iluvpomeranians/Acoustic_Imager/src/hardware/component_step_files/M4_Fan_screw_8mm.step

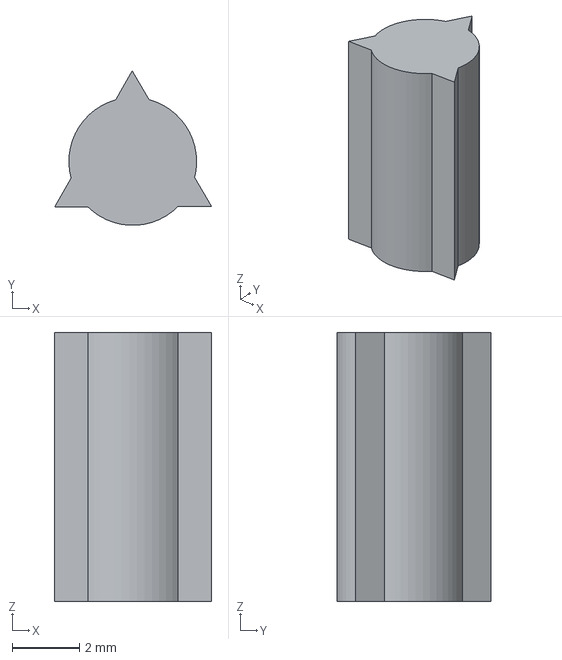
[picture p15: CAD file, 2026-03-14]
src/hardware/component_step_files/M4_Fan_screw_8mm.step
4.67 x 4.59 x 8.00 mm
