iluvpomeranians/Acoustic_Imager/src/hardware/component_step_files/M3.5x8mm Screw Hole Positive-Body.step

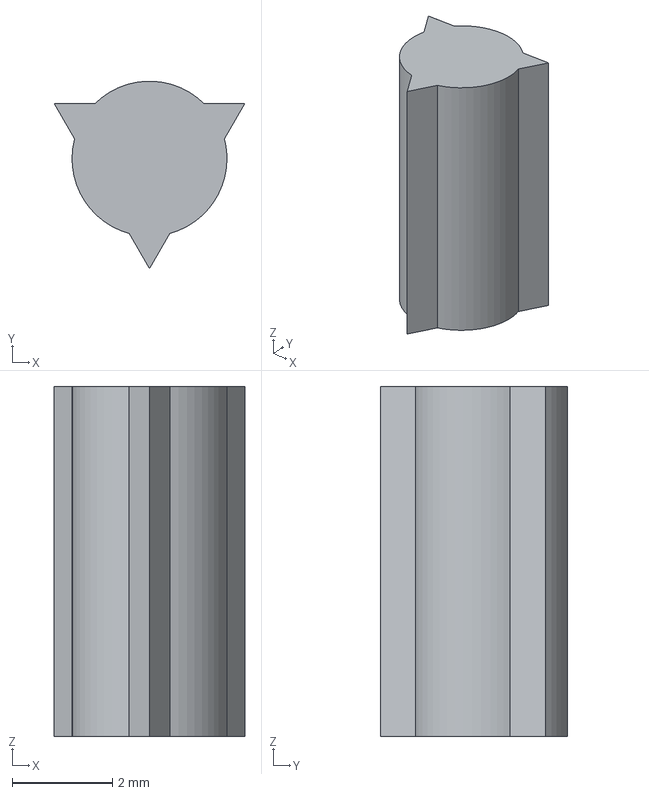
[picture p16: CAD file, 2026-03-14]
src/hardware/component_step_files/M3.5x8mm Screw Hole Positive-Body.step
3.81 x 3.75 x 7.00 mm
