iluvpomeranians/Acoustic_Imager/src/firmware/STM32G4_Cap/src/CubeMX/Core/Src/main.c

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
/* Includes ------------------------------------------------------------------*/
#include "main.h"
#include "adc.h"
#include "dma.h"
#include "spi.h"
#include "tim.h"
#include "usart.h"
#include "usb_device.h"
#include "gpio.h"

/* USER CODE BEGIN Includes */
#include "app_main.h"
/* USER CODE END Includes */


void SystemClock_Config(void);
/* USER CODE BEGIN 0 */


// HAL_SYSCFG_VREFBUF_HighImpedanceConfig(SYSCFG_VREFBUF_HIGH_IMPEDANCE_DISABLE);
// HAL_SYSCFG_EnableVREFBUF();
// IMPORTANT FOR ADC VALUES, DO NOT CHANGE
//C:\Users\Fabz\Desktop\aroundfuckin\Capstone_490_Software\src\firmware\STM32G4_Cap\src\CubeMX\Core\Src\stm32g4xx_hal_msp.c




/* USER CODE END 0 */

/**
  * @brief  The application entry point.
  * @retval int
  */
int main(void)
{

  /* MCU Configuration--------------------------------------------------------*/

  /* Reset of all peripherals, Initializes the Flash interface and the Systick. */
  HAL_Init();

  /* Configure the system clock */
  SystemClock_Config();

  /* USER CODE BEGIN SysInit */
  // TODO: TEST the UART and USB init
  /* USER CODE END SysInit */

  /* Initialize all configured peripherals */
  MX_GPIO_Init();
  MX_DMA_Init();
  MX_ADC1_Init();
  MX_ADC2_Init();
  MX_ADC3_Init();
  MX_ADC4_Init();
  MX_SPI4_Init();
  MX_TIM6_Init();
  MX_USART2_UART_Init();
  MX_USB_Device_Init();
  MX_ADC5_Init();
  /* USER CODE BEGIN 2 */
  app_init();
  app_start();
  /* USER CODE END 2 */

  /* Infinite loop */
  /* USER CODE BEGIN WHILE */
  while (1)
  {
    /* USER CODE END WHILE */

    /* USER CODE BEGIN 3 */
#if MODE == RELEASE | MODE == DEBUG
    app_loop();
#elif MODE == TEST_SPI_STREAM
    test_spi_stream_loop();
#elif MODE == TEST_DSP_PIPELINE
    test_dsp_pipeline_loop();
#endif
  }
  
  /* USER CODE END 3 */
}

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
