iluvpomeranians/Acoustic_Imager/src/firmware/STM32G4_Cap/src/CubeMX/App/app_main.h

#ifndef APP_MAIN_H
#define APP_MAIN_H

#ifdef __cplusplus
extern "C" {
#endif

/* =========================================================================
 * INCLUDES
 * ========================================================================= */
#include <stdint.h>
#include <stdbool.h>

/* =========================================================================
 * DEFINES
 * ========================================================================= */
#define APP_VERSION "1.0.0"

#define FRAME_SIZE 512
#define N_ADCS 4
#define N_CH_PER_ADC 4
#define N_MICS 16



// TODO: Consider discarding Nyquist bin (bin 512)
#define N_BINS ((FRAME_SIZE >> 1) + 1) // For real FFT: N_BINS = (N/2)+1 = 513 

#define APP_USB_CMD_MAX_LEN 64u

// Battery is measured through a 6:1 divider, so scale sensed pin voltage back to pack voltage.
#define BATT_ADC_VREF_MV 2900u
#define BATT_DIVIDER_NUMERATOR 5.97
#define BATT_DIVIDER_DENOMINATOR 1u

// Cycle-reduction options (see App/OPTIMIZATION_PLAN.md)
#define SPI_CHECKSUM_ENABLE       0   /* 0 = no checksum (~300k CC/frame saved); host must use header+payload only */
#define APP_BATTERY_READ_EVERY_N_FRAMES 8u   /* Read battery every N frames; use cached value otherwise (~100k CC saved when N>1) */
#define APP_CLIP_DETECT_ENABLE    0   /* 0 = skip time-domain clipping scan every frame */

// Configuration defines
#define SPI_SINGLE_MIC 0
#define SPI_FULL_FRAME 1
#define SPI_MODE SPI_FULL_FRAME

#define RELEASE 0
#define TEST_SPI_STREAM 1
#define TEST_DSP_PIPELINE 2
#define DEBUG 3

#define MODE RELEASE

// Float print helper macros
#define PRINT_F1(x) ((int)((x) * 10.0f) / 10),  ((int)((x) * 10.0f) % 10)
#define PRINT_F2(x) ((int)((x) * 100.0f) / 100), ((int)((x) * 100.0f) % 100)
#define PRINT_F3(x) ((int)((x) * 1000.0f) / 1000), ((int)((x) * 1000.0f) % 1000)

/* =========================================================================
 * TYPE DEFINITIONS
 * ========================================================================= */
typedef enum {
    APP_STATE_IDLE,
    APP_STATE_RUNNING,
    APP_STATE_ERROR
} app_state_t;

/* =========================================================================
 * FUNCTION PROTOTYPES
 * ========================================================================= */
void app_init(void);
void app_start(void);
void app_loop(void);
void app_usb_cdc_rx(const uint8_t *buf, uint32_t len);
// void app_handle_error(uint32_t error_code);

// Unit test loops
void test_spi_stream_loop(void);
void test_dsp_pipeline_loop(void);

#ifdef __cplusplus
}
#endif

#endif /* APP_MAIN_H */
