iluvpomeranians/Acoustic_Imager/src/firmware/STM32G4_Cap/src/CubeMX/Core/Inc/main.h

#define GAIN_CNTL_Pin GPIO_PIN_9
#define GAIN_CNTL_GPIO_Port GPIOD
#define BATT_SAMPLE_Pin GPIO_PIN_8
#define BATT_SAMPLE_GPIO_Port GPIOA
#define AUTO_GAIN_CNTL_Pin GPIO_PIN_9
#define AUTO_GAIN_CNTL_GPIO_Port GPIOB
#define MCU_STATUS_Pin GPIO_PIN_0
#define MCU_STATUS_GPIO_Port GPIOE
#define RPI_STATUS_Pin GPIO_PIN_1
#define RPI_STATUS_GPIO_Port GPIOE
