iluvpomeranians/Acoustic_Imager/src/firmware/STM32G4_Cap/src/CubeMX/Core/Src/adc.c

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
/* Includes ------------------------------------------------------------------*/
#include "adc.h"

/* USER CODE BEGIN 0 */
static volatile uint8_t adc_half_ready = 0;
static volatile uint8_t adc_full_ready = 0;

uint8_t ADC_HalfReady(void)      { return adc_half_ready; }
uint8_t ADC_FullReady(void)      { return adc_full_ready; }
void    ADC_ClearHalfReady(void) { adc_half_ready = 0; }
void    ADC_ClearFullReady(void) { adc_full_ready = 0; }

HAL_StatusTypeDef ADC_ReadBatteryRaw(uint16_t *raw_counts)
{
  if (!raw_counts) {
    return HAL_ERROR;
  }

  if (HAL_ADC_Start(&hadc5) != HAL_OK) {
    return HAL_ERROR;
  }

  if (HAL_ADC_PollForConversion(&hadc5, 10u) != HAL_OK) {
    (void)HAL_ADC_Stop(&hadc5);
    return HAL_TIMEOUT;
  }

  *raw_counts = (uint16_t)HAL_ADC_GetValue(&hadc5);
  return HAL_ADC_Stop(&hadc5);
}

/* USER CODE END 0 */

ADC_HandleTypeDef hadc1;
ADC_HandleTypeDef hadc2;
ADC_HandleTypeDef hadc3;
ADC_HandleTypeDef hadc4;
ADC_HandleTypeDef hadc5;
DMA_HandleTypeDef hdma_adc1;
DMA_HandleTypeDef hdma_adc2;
DMA_HandleTypeDef hdma_adc3;
DMA_HandleTypeDef hdma_adc4;

/* ADC1 init function */
void MX_ADC1_Init(void)
{

  ADC_MultiModeTypeDef multimode = {0};
  ADC_ChannelConfTypeDef sConfig = {0};

  /** Common config
  */
  hadc1.Instance = ADC1;
  hadc1.Init.ClockPrescaler = ADC_CLOCK_SYNC_PCLK_DIV4;
  hadc1.Init.Resolution = ADC_RESOLUTION_12B;
  hadc1.Init.DataAlign = ADC_DATAALIGN_RIGHT;
  hadc1.Init.GainCompensation = 0;
  hadc1.Init.ScanConvMode = ADC_SCAN_ENABLE;
  hadc1.Init.EOCSelection = ADC_EOC_SINGLE_CONV;
  hadc1.Init.LowPowerAutoWait = DISABLE;
  hadc1.Init.ContinuousConvMode = DISABLE;
  hadc1.Init.NbrOfConversion = 4;
  hadc1.Init.DiscontinuousConvMode = DISABLE;
  hadc1.Init.ExternalTrigConv = ADC_EXTERNALTRIG_T6_TRGO;
  hadc1.Init.ExternalTrigConvEdge = ADC_EXTERNALTRIGCONVEDGE_RISING;
  hadc1.Init.DMAContinuousRequests = ENABLE;
  hadc1.Init.Overrun = ADC_OVR_DATA_OVERWRITTEN;
  hadc1.Init.OversamplingMode = DISABLE;
  if (HAL_ADC_Init(&hadc1) != HAL_OK)
  {
    Error_Handler();
  }

  /** Configure the ADC multi-mode
  */
  multimode.Mode = ADC_MODE_INDEPENDENT;
  if (HAL_ADCEx_MultiModeConfigChannel(&hadc1, &multimode) != HAL_OK)
  {
    Error_Handler();
  }

  /** Configure Regular Channel
  */
  sConfig.Channel = ADC_CHANNEL_1;
  sConfig.Rank = ADC_REGULAR_RANK_1;
  sConfig.SamplingTime = ADC_SAMPLETIME_12CYCLES_5;
  sConfig.SingleDiff = ADC_SINGLE_ENDED;
  sConfig.OffsetNumber = ADC_OFFSET_NONE;
  sConfig.Offset = 0;
  if (HAL_ADC_ConfigChannel(&hadc1, &sConfig) != HAL_OK)
  {
    Error_Handler();
  }

  /** Configure Regular Channel
  */
  sConfig.Channel = ADC_CHANNEL_2;
  sConfig.Rank = ADC_REGULAR_RANK_2;
  if (HAL_ADC_ConfigChannel(&hadc1, &sConfig) != HAL_OK)
  {
    Error_Handler();
  }

  /** Configure Regular Channel
  */
  sConfig.Channel = ADC_CHANNEL_3;
  sConfig.Rank = ADC_REGULAR_RANK_3;
  if (HAL_ADC_ConfigChannel(&hadc1, &sConfig) != HAL_OK)
  {
    Error_Handler();
  }

  /** Configure Regular Channel
  */
  sConfig.Channel = ADC_CHANNEL_4;
  sConfig.Rank = ADC_REGULAR_RANK_4;
  if (HAL_ADC_ConfigChannel(&hadc1, &sConfig) != HAL_OK)
  {
    Error_Handler();
  }
}
/* ADC2 init function */
void MX_ADC2_Init(void)
{

  ADC_ChannelConfTypeDef sConfig = {0};

  /** Common config
  */
  hadc2.Instance = ADC2;
  hadc2.Init.ClockPrescaler = ADC_CLOCK_SYNC_PCLK_DIV4;
  hadc2.Init.Resolution = ADC_RESOLUTION_12B;
  hadc2.Init.DataAlign = ADC_DATAALIGN_RIGHT;
  hadc2.Init.GainCompensation = 0;
  hadc2.Init.ScanConvMode = ADC_SCAN_ENABLE;
  hadc2.Init.EOCSelection = ADC_EOC_SINGLE_CONV;
  hadc2.Init.LowPowerAutoWait = DISABLE;
  hadc2.Init.ContinuousConvMode = DISABLE;
  hadc2.Init.NbrOfConversion = 4;
  hadc2.Init.DiscontinuousConvMode = DISABLE;
  hadc2.Init.ExternalTrigConv = ADC_EXTERNALTRIG_T6_TRGO;
  hadc2.Init.ExternalTrigConvEdge = ADC_EXTERNALTRIGCONVEDGE_RISING;
  hadc2.Init.DMAContinuousRequests = ENABLE;
  hadc2.Init.Overrun = ADC_OVR_DATA_OVERWRITTEN;
  hadc2.Init.OversamplingMode = DISABLE;
  if (HAL_ADC_Init(&hadc2) != HAL_OK)
  {
    Error_Handler();
  }

  /** Configure Regular Channel
  */
  sConfig.Channel = ADC_CHANNEL_3;
  sConfig.Rank = ADC_REGULAR_RANK_1;
  sConfig.SamplingTime = ADC_SAMPLETIME_12CYCLES_5;
  sConfig.SingleDiff = ADC_SINGLE_ENDED;
  sConfig.OffsetNumber = ADC_OFFSET_NONE;
  sConfig.Offset = 0;
  if (HAL_ADC_ConfigChannel(&hadc2, &sConfig) != HAL_OK)
  {
    Error_Handler();
  }

  /** Configure Regular Channel
  */
  sConfig.Channel = ADC_CHANNEL_4;
  sConfig.Rank = ADC_REGULAR_RANK_2;
  if (HAL_ADC_ConfigChannel(&hadc2, &sConfig) != HAL_OK)
  {
    Error_Handler();
  }

  /** Configure Regular Channel
  */
  sConfig.Channel = ADC_CHANNEL_5;
  sConfig.Rank = ADC_REGULAR_RANK_3;
  if (HAL_ADC_ConfigChannel(&hadc2, &sConfig) != HAL_OK)
  {
    Error_Handler();
  }

  /** Configure Regular Channel
  */
  sConfig.Channel = ADC_CHANNEL_6;
  sConfig.Rank = ADC_REGULAR_RANK_4;
  if (HAL_ADC_ConfigChannel(&hadc2, &sConfig) != HAL_OK)
  {
    Error_Handler();
  }
}
/* ADC3 init function */
void MX_ADC3_Init(void)
{

  ADC_MultiModeTypeDef multimode = {0};
  ADC_ChannelConfTypeDef sConfig = {0};

  /** Common config
  */
  hadc3.Instance = ADC3;
  hadc3.Init.ClockPrescaler = ADC_CLOCK_SYNC_PCLK_DIV4;
  hadc3.Init.Resolution = ADC_RESOLUTION_12B;
  hadc3.Init.DataAlign = ADC_DATAALIGN_RIGHT;
  hadc3.Init.GainCompensation = 0;
  hadc3.Init.ScanConvMode = ADC_SCAN_ENABLE;
  hadc3.Init.EOCSelection = ADC_EOC_SINGLE_CONV;
  hadc3.Init.LowPowerAutoWait = DISABLE;
  hadc3.Init.ContinuousConvMode = DISABLE;
  hadc3.Init.NbrOfConversion = 4;
  hadc3.Init.DiscontinuousConvMode = DISABLE;
  hadc3.Init.ExternalTrigConv = ADC_EXTERNALTRIG_T6_TRGO;
  hadc3.Init.ExternalTrigConvEdge = ADC_EXTERNALTRIGCONVEDGE_RISING;
  hadc3.Init.DMAContinuousRequests = ENABLE;
  hadc3.Init.Overrun = ADC_OVR_DATA_OVERWRITTEN;
  hadc3.Init.OversamplingMode = DISABLE;
  if (HAL_ADC_Init(&hadc3) != HAL_OK)
  {
    Error_Handler();
  }

  /** Configure the ADC multi-mode
  */
  multimode.Mode = ADC_MODE_INDEPENDENT;
  if (HAL_ADCEx_MultiModeConfigChannel(&hadc3, &multimode) != HAL_OK)
  {
    Error_Handler();
  }

  /** Configure Regular Channel
  */
  sConfig.Channel = ADC_CHANNEL_1;
  sConfig.Rank = ADC_REGULAR_RANK_1;
  sConfig.SamplingTime = ADC_SAMPLETIME_12CYCLES_5;
  sConfig.SingleDiff = ADC_SINGLE_ENDED;
  sConfig.OffsetNumber = ADC_OFFSET_NONE;
  sConfig.Offset = 0;
  if (HAL_ADC_ConfigChannel(&hadc3, &sConfig) != HAL_OK)
  {
    Error_Handler();
  }

  /** Configure Regular Channel
  */
  sConfig.Channel = ADC_CHANNEL_2;
  sConfig.Rank = ADC_REGULAR_RANK_2;
  if (HAL_ADC_ConfigChannel(&hadc3, &sConfig) != HAL_OK)
  {
    Error_Handler();
  }

  /** Configure Regular Channel
  */
  sConfig.Channel = ADC_CHANNEL_3;
  sConfig.Rank = ADC_REGULAR_RANK_3;
  if (HAL_ADC_ConfigChannel(&hadc3, &sConfig) != HAL_OK)
  {
    Error_Handler();
  }

  /** Configure Regular Channel
  */
  sConfig.Channel = ADC_CHANNEL_4;
  sConfig.Rank = ADC_REGULAR_RANK_4;
  if (HAL_ADC_ConfigChannel(&hadc3, &sConfig) != HAL_OK)
  {
    Error_Handler();
  }
}
/* ADC4 init function */
void MX_ADC4_Init(void)
{

  ADC_ChannelConfTypeDef sConfig = {0};

  /** Common config
  */
  hadc4.Instance = ADC4;
  hadc4.Init.ClockPrescaler = ADC_CLOCK_SYNC_PCLK_DIV4;
  hadc4.Init.Resolution = ADC_RESOLUTION_12B;
  hadc4.Init.DataAlign = ADC_DATAALIGN_RIGHT;
  hadc4.Init.GainCompensation = 0;
  hadc4.Init.ScanConvMode = ADC_SCAN_ENABLE;
  hadc4.Init.EOCSelection = ADC_EOC_SINGLE_CONV;
  hadc4.Init.LowPowerAutoWait = DISABLE;
  hadc4.Init.ContinuousConvMode = DISABLE;
  hadc4.Init.NbrOfConversion = 4;
  hadc4.Init.DiscontinuousConvMode = DISABLE;
  hadc4.Init.ExternalTrigConv = ADC_EXTERNALTRIG_T6_TRGO;
  hadc4.Init.ExternalTrigConvEdge = ADC_EXTERNALTRIGCONVEDGE_RISING;
  hadc4.Init.DMAContinuousRequests = ENABLE;
  hadc4.Init.Overrun = ADC_OVR_DATA_OVERWRITTEN;
  hadc4.Init.OversamplingMode = DISABLE;
  if (HAL_ADC_Init(&hadc4) != HAL_OK)
  {
    Error_Handler();
  }

  /** Configure Regular Channel
  */
  sConfig.Channel = ADC_CHANNEL_1;
  sConfig.Rank = ADC_REGULAR_RANK_1;
  sConfig.SamplingTime = ADC_SAMPLETIME_12CYCLES_5;
  sConfig.SingleDiff = ADC_SINGLE_ENDED;
  sConfig.OffsetNumber = ADC_OFFSET_NONE;
  sConfig.Offset = 0;
  if (HAL_ADC_ConfigChannel(&hadc4, &sConfig) != HAL_OK)
  {
    Error_Handler();
  }

  /** Configure Regular Channel
  */
  sConfig.Channel = ADC_CHANNEL_2;
  sConfig.Rank = ADC_REGULAR_RANK_2;
  if (HAL_ADC_ConfigChannel(&hadc4, &sConfig) != HAL_OK)
  {
    Error_Handler();
  }

  /** Configure Regular Channel
  */
  sConfig.Channel = ADC_CHANNEL_3;
  sConfig.Rank = ADC_REGULAR_RANK_3;
  if (HAL_ADC_ConfigChannel(&hadc4, &sConfig) != HAL_OK)
  {
    Error_Handler();
  }

  /** Configure Regular Channel
  */
  sConfig.Channel = ADC_CHANNEL_4;
  sConfig.Rank = ADC_REGULAR_RANK_4;
  if (HAL_ADC_ConfigChannel(&hadc4, &sConfig) != HAL_OK)
  {
    Error_Handler();
  }
}
/* ADC5 init function */
void MX_ADC5_Init(void)
{

  ADC_ChannelConfTypeDef sConfig = {0};

  /** Common config
  */
  hadc5.Instance = ADC5;
  hadc5.Init.ClockPrescaler = ADC_CLOCK_SYNC_PCLK_DIV4;
  hadc5.Init.Resolution = ADC_RESOLUTION_12B;
  hadc5.Init.DataAlign = ADC_DATAALIGN_RIGHT;
  hadc5.Init.GainCompensation = 0;
  hadc5.Init.ScanConvMode = ADC_SCAN_DISABLE;
  hadc5.Init.EOCSelection = ADC_EOC_SINGLE_CONV;
  hadc5.Init.LowPowerAutoWait = DISABLE;
  hadc5.Init.ContinuousConvMode = DISABLE;
  hadc5.Init.NbrOfConversion = 1;
  hadc5.Init.DiscontinuousConvMode = DISABLE;
  hadc5.Init.ExternalTrigConv = ADC_SOFTWARE_START;
  hadc5.Init.ExternalTrigConvEdge = ADC_EXTERNALTRIGCONVEDGE_NONE;
  hadc5.Init.DMAContinuousRequests = DISABLE;
  hadc5.Init.Overrun = ADC_OVR_DATA_PRESERVED;
  hadc5.Init.OversamplingMode = DISABLE;
  if (HAL_ADC_Init(&hadc5) != HAL_OK)
  {
    Error_Handler();
  }

  /** Configure Regular Channel
  */
  sConfig.Channel = ADC_CHANNEL_1;
  sConfig.Rank = ADC_REGULAR_RANK_1;
  sConfig.SamplingTime = ADC_SAMPLETIME_2CYCLES_5;
  sConfig.SingleDiff = ADC_SINGLE_ENDED;
  sConfig.OffsetNumber = ADC_OFFSET_NONE;
  sConfig.Offset = 0;
  if (HAL_ADC_ConfigChannel(&hadc5, &sConfig) != HAL_OK)
  {
    Error_Handler();
  }
}

static uint32_t HAL_RCC_ADC12_CLK_ENABLED=0;
static uint32_t HAL_RCC_ADC345_CLK_ENABLED=0;

void HAL_ADC_MspInit(ADC_HandleTypeDef* adcHandle)
{

  GPIO_InitTypeDef GPIO_InitStruct = {0};
  RCC_PeriphCLKInitTypeDef PeriphClkInit = {0};
  if(adcHandle->Instance==ADC1)
  {
  /** Initializes the peripherals clocks
  */
    PeriphClkInit.PeriphClockSelection = RCC_PERIPHCLK_ADC12;
    PeriphClkInit.Adc12ClockSelection = RCC_ADC12CLKSOURCE_SYSCLK;
    if (HAL_RCCEx_PeriphCLKConfig(&PeriphClkInit) != HAL_OK)
    {
      Error_Handler();
    }

    /* ADC1 clock enable */
    HAL_RCC_ADC12_CLK_ENABLED++;
    if(HAL_RCC_ADC12_CLK_ENABLED==1){
      __HAL_RCC_ADC12_CLK_ENABLE();
    }

    __HAL_RCC_GPIOA_CLK_ENABLE();
    /**ADC1 GPIO Configuration
    PA0     ------> ADC1_IN1
    PA1     ------> ADC1_IN2
    PA2     ------> ADC1_IN3
    PA3     ------> ADC1_IN4
    */
    GPIO_InitStruct.Pin = GPIO_PIN_0|GPIO_PIN_1|GPIO_PIN_2|GPIO_PIN_3;
    GPIO_InitStruct.Mode = GPIO_MODE_ANALOG;
    GPIO_InitStruct.Pull = GPIO_NOPULL;
    HAL_GPIO_Init(GPIOA, &GPIO_InitStruct);

    /* ADC1 DMA Init */
    /* ADC1 Init */
    hdma_adc1.Instance = DMA1_Channel1;
    hdma_adc1.Init.Request = DMA_REQUEST_ADC1;
    hdma_adc1.Init.Direction = DMA_PERIPH_TO_MEMORY;
    hdma_adc1.Init.PeriphInc = DMA_PINC_DISABLE;
    hdma_adc1.Init.MemInc = DMA_MINC_ENABLE;
    hdma_adc1.Init.PeriphDataAlignment = DMA_PDATAALIGN_HALFWORD;
    hdma_adc1.Init.MemDataAlignment = DMA_MDATAALIGN_HALFWORD;
    hdma_adc1.Init.Mode = DMA_CIRCULAR;
    hdma_adc1.Init.Priority = DMA_PRIORITY_LOW;
    if (HAL_DMA_Init(&hdma_adc1) != HAL_OK)
    {
      Error_Handler();
    }

    __HAL_LINKDMA(adcHandle,DMA_Handle,hdma_adc1);

    /* ADC1 interrupt Init */
    HAL_NVIC_SetPriority(ADC1_2_IRQn, 0, 0);
    HAL_NVIC_EnableIRQ(ADC1_2_IRQn);
  }
  else if(adcHandle->Instance==ADC2)
  {
  /** Initializes the peripherals clocks
  */
    PeriphClkInit.PeriphClockSelection = RCC_PERIPHCLK_ADC12;
    PeriphClkInit.Adc12ClockSelection = RCC_ADC12CLKSOURCE_SYSCLK;
    if (HAL_RCCEx_PeriphCLKConfig(&PeriphClkInit) != HAL_OK)
    {
      Error_Handler();
    }

    /* ADC2 clock enable */
    HAL_RCC_ADC12_CLK_ENABLED++;
    if(HAL_RCC_ADC12_CLK_ENABLED==1){
      __HAL_RCC_ADC12_CLK_ENABLE();
    }

    __HAL_RCC_GPIOC_CLK_ENABLE();
    __HAL_RCC_GPIOA_CLK_ENABLE();
    /**ADC2 GPIO Configuration
    PC0     ------> ADC2_IN6
    PA6     ------> ADC2_IN3
    PA7     ------> ADC2_IN4
    PC4     ------> ADC2_IN5
    */
    GPIO_InitStruct.Pin = GPIO_PIN_0|GPIO_PIN_4;
    GPIO_InitStruct.Mode = GPIO_MODE_ANALOG;
    GPIO_InitStruct.Pull = GPIO_NOPULL;
    HAL_GPIO_Init(GPIOC, &GPIO_InitStruct);

    GPIO_InitStruct.Pin = GPIO_PIN_6|GPIO_PIN_7;
    GPIO_InitStruct.Mode = GPIO_MODE_ANALOG;
    GPIO_InitStruct.Pull = GPIO_NOPULL;
    HAL_GPIO_Init(GPIOA, &GPIO_InitStruct);

    /* ADC2 DMA Init */
    /* ADC2 Init */
    hdma_adc2.Instance = DMA1_Channel2;
    hdma_adc2.Init.Request = DMA_REQUEST_ADC2;
    hdma_adc2.Init.Direction = DMA_PERIPH_TO_MEMORY;
    hdma_adc2.Init.PeriphInc = DMA_PINC_DISABLE;
    hdma_adc2.Init.MemInc = DMA_MINC_ENABLE;
    hdma_adc2.Init.PeriphDataAlignment = DMA_PDATAALIGN_HALFWORD;
    hdma_adc2.Init.MemDataAlignment = DMA_MDATAALIGN_HALFWORD;
    hdma_adc2.Init.Mode = DMA_CIRCULAR;
    hdma_adc2.Init.Priority = DMA_PRIORITY_LOW;
    if (HAL_DMA_Init(&hdma_adc2) != HAL_OK)
    {
      Error_Handler();
    }

    __HAL_LINKDMA(adcHandle,DMA_Handle,hdma_adc2);

    /* ADC2 interrupt Init */
    HAL_NVIC_SetPriority(ADC1_2_IRQn, 0, 0);
    HAL_NVIC_EnableIRQ(ADC1_2_IRQn);
  }
  else if(adcHandle->Instance==ADC3)
  {
  /** Initializes the peripherals clocks
  */
    PeriphClkInit.PeriphClockSelection = RCC_PERIPHCLK_ADC345;
    PeriphClkInit.Adc345ClockSelection = RCC_ADC345CLKSOURCE_SYSCLK;
    if (HAL_RCCEx_PeriphCLKConfig(&PeriphClkInit) != HAL_OK)
    {
      Error_Handler();
    }

    /* ADC3 clock enable */
    HAL_RCC_ADC345_CLK_ENABLED++;
    if(HAL_RCC_ADC345_CLK_ENABLED==1){
      __HAL_RCC_ADC345_CLK_ENABLE();
    }

    __HAL_RCC_GPIOB_CLK_ENABLE();
    __HAL_RCC_GPIOE_CLK_ENABLE();
    /**ADC3 GPIO Configuration
    PB1     ------> ADC3_IN1
    PE7     ------> ADC3_IN4
    PE9     ------> ADC3_IN2
    PE13     ------> ADC3_IN3
    */
    GPIO_InitStruct.Pin = GPIO_PIN_1;
    GPIO_InitStruct.Mode = GPIO_MODE_ANALOG;
    GPIO_InitStruct.Pull = GPIO_NOPULL;
    HAL_GPIO_Init(GPIOB, &GPIO_InitStruct);

    GPIO_InitStruct.Pin = GPIO_PIN_7|GPIO_PIN_9|GPIO_PIN_13;
    GPIO_InitStruct.Mode = GPIO_MODE_ANALOG;
    GPIO_InitStruct.Pull = GPIO_NOPULL;
    HAL_GPIO_Init(GPIOE, &GPIO_InitStruct);

    /* ADC3 DMA Init */
    /* ADC3 Init */
    hdma_adc3.Instance = DMA1_Channel3;
    hdma_adc3.Init.Request = DMA_REQUEST_ADC3;
    hdma_adc3.Init.Direction = DMA_PERIPH_TO_MEMORY;
    hdma_adc3.Init.PeriphInc = DMA_PINC_DISABLE;
    hdma_adc3.Init.MemInc = DMA_MINC_ENABLE;
    hdma_adc3.Init.PeriphDataAlignment = DMA_PDATAALIGN_HALFWORD;
    hdma_adc3.Init.MemDataAlignment = DMA_MDATAALIGN_HALFWORD;
    hdma_adc3.Init.Mode = DMA_CIRCULAR;
    hdma_adc3.Init.Priority = DMA_PRIORITY_LOW;
    if (HAL_DMA_Init(&hdma_adc3) != HAL_OK)
    {
      Error_Handler();
    }

    __HAL_LINKDMA(adcHandle,DMA_Handle,hdma_adc3);

    /* ADC3 interrupt Init */
    HAL_NVIC_SetPriority(ADC3_IRQn, 0, 0);
    HAL_NVIC_EnableIRQ(ADC3_IRQn);
  }
  else if(adcHandle->Instance==ADC4)
  {
  /** Initializes the peripherals clocks
  */
    PeriphClkInit.PeriphClockSelection = RCC_PERIPHCLK_ADC345;
    PeriphClkInit.Adc345ClockSelection = RCC_ADC345CLKSOURCE_SYSCLK;
    if (HAL_RCCEx_PeriphCLKConfig(&PeriphClkInit) != HAL_OK)
    {
      Error_Handler();
    }

    /* ADC4 clock enable */
    HAL_RCC_ADC345_CLK_ENABLED++;
    if(HAL_RCC_ADC345_CLK_ENABLED==1){
      __HAL_RCC_ADC345_CLK_ENABLE();
    }

    __HAL_RCC_GPIOE_CLK_ENABLE();
    __HAL_RCC_GPIOB_CLK_ENABLE();
    /**ADC4 GPIO Configuration
    PE14     ------> ADC4_IN1
    PE15     ------> ADC4_IN2
    PB12     ------> ADC4_IN3
    PB14     ------> ADC4_IN4
    */
    GPIO_InitStruct.Pin = GPIO_PIN_14|GPIO_PIN_15;
    GPIO_InitStruct.Mode = GPIO_MODE_ANALOG;
    GPIO_InitStruct.Pull = GPIO_NOPULL;
    HAL_GPIO_Init(GPIOE, &GPIO_InitStruct);

    GPIO_InitStruct.Pin = GPIO_PIN_12|GPIO_PIN_14;
    GPIO_InitStruct.Mode = GPIO_MODE_ANALOG;
    GPIO_InitStruct.Pull = GPIO_NOPULL;
    HAL_GPIO_Init(GPIOB, &GPIO_InitStruct);

    /* ADC4 DMA Init */
    /* ADC4 Init */
    hdma_adc4.Instance = DMA1_Channel4;
    hdma_adc4.Init.Request = DMA_REQUEST_ADC4;
    hdma_adc4.Init.Direction = DMA_PERIPH_TO_MEMORY;
    hdma_adc4.Init.PeriphInc = DMA_PINC_DISABLE;
    hdma_adc4.Init.MemInc = DMA_MINC_ENABLE;
    hdma_adc4.Init.PeriphDataAlignment = DMA_PDATAALIGN_HALFWORD;
    hdma_adc4.Init.MemDataAlignment = DMA_MDATAALIGN_HALFWORD;
    hdma_adc4.Init.Mode = DMA_CIRCULAR;
    hdma_adc4.Init.Priority = DMA_PRIORITY_LOW;
    if (HAL_DMA_Init(&hdma_adc4) != HAL_OK)
    {
      Error_Handler();
    }

    __HAL_LINKDMA(adcHandle,DMA_Handle,hdma_adc4);

    /* ADC4 interrupt Init */
    HAL_NVIC_SetPriority(ADC4_IRQn, 0, 0);
    HAL_NVIC_EnableIRQ(ADC4_IRQn);
  }
  else if(adcHandle->Instance==ADC5)
  {
  /** Initializes the peripherals clocks
  */
    PeriphClkInit.PeriphClockSelection = RCC_PERIPHCLK_ADC345;
    PeriphClkInit.Adc345ClockSelection = RCC_ADC345CLKSOURCE_SYSCLK;
    if (HAL_RCCEx_PeriphCLKConfig(&PeriphClkInit) != HAL_OK)
    {
      Error_Handler();
    }

    /* ADC5 clock enable */
    HAL_RCC_ADC345_CLK_ENABLED++;
    if(HAL_RCC_ADC345_CLK_ENABLED==1){
      __HAL_RCC_ADC345_CLK_ENABLE();
    }

    __HAL_RCC_GPIOA_CLK_ENABLE();
    /**ADC5 GPIO Configuration
    PA8     ------> ADC5_IN1
    */
    GPIO_InitStruct.Pin = BATT_SAMPLE_Pin;
    GPIO_InitStruct.Mode = GPIO_MODE_ANALOG;
    GPIO_InitStruct.Pull = GPIO_NOPULL;
    HAL_GPIO_Init(BATT_SAMPLE_GPIO_Port, &GPIO_InitStruct);

  }
}

void HAL_ADC_MspDeInit(ADC_HandleTypeDef* adcHandle)
{

  if(adcHandle->Instance==ADC1)
  {
    /* Peripheral clock disable */
    HAL_RCC_ADC12_CLK_ENABLED--;
    if(HAL_RCC_ADC12_CLK_ENABLED==0){
      __HAL_RCC_ADC12_CLK_DISABLE();
    }

    /**ADC1 GPIO Configuration
    PA0     ------> ADC1_IN1
    PA1     ------> ADC1_IN2
    PA2     ------> ADC1_IN3
    PA3     ------> ADC1_IN4
    */
    HAL_GPIO_DeInit(GPIOA, GPIO_PIN_0|GPIO_PIN_1|GPIO_PIN_2|GPIO_PIN_3);

    /* ADC1 DMA DeInit */
    HAL_DMA_DeInit(adcHandle->DMA_Handle);

    /* ADC1 interrupt Deinit */
  /* USER CODE BEGIN ADC1:ADC1_2_IRQn disable */
    /**
    * Uncomment the line below to disable the "ADC1_2_IRQn" interrupt
    * Be aware, disabling shared interrupt may affect other IPs
    */
    /* HAL_NVIC_DisableIRQ(ADC1_2_IRQn); */
  /* USER CODE END ADC1:ADC1_2_IRQn disable */

  }
  else if(adcHandle->Instance==ADC2)
  {
    /* Peripheral clock disable */
    HAL_RCC_ADC12_CLK_ENABLED--;
    if(HAL_RCC_ADC12_CLK_ENABLED==0){
      __HAL_RCC_ADC12_CLK_DISABLE();
    }

    /**ADC2 GPIO Configuration
    PC0     ------> ADC2_IN6
    PA6     ------> ADC2_IN3
    PA7     ------> ADC2_IN4
    PC4     ------> ADC2_IN5
    */
    HAL_GPIO_DeInit(GPIOC, GPIO_PIN_0|GPIO_PIN_4);

    HAL_GPIO_DeInit(GPIOA, GPIO_PIN_6|GPIO_PIN_7);

    /* ADC2 DMA DeInit */
    HAL_DMA_DeInit(adcHandle->DMA_Handle);

    /* ADC2 interrupt Deinit */
  /* USER CODE BEGIN ADC2:ADC1_2_IRQn disable */
    /**
    * Uncomment the line below to disable the "ADC1_2_IRQn" interrupt
    * Be aware, disabling shared interrupt may affect other IPs
    */
    /* HAL_NVIC_DisableIRQ(ADC1_2_IRQn); */
  /* USER CODE END ADC2:ADC1_2_IRQn disable */

  }
  else if(adcHandle->Instance==ADC3)
  {
    /* Peripheral clock disable */
    HAL_RCC_ADC345_CLK_ENABLED--;
    if(HAL_RCC_ADC345_CLK_ENABLED==0){
      __HAL_RCC_ADC345_CLK_DISABLE();
    }

    /**ADC3 GPIO Configuration
    PB1     ------> ADC3_IN1
    PE7     ------> ADC3_IN4
    PE9     ------> ADC3_IN2
    PE13     ------> ADC3_IN3
    */
    HAL_GPIO_DeInit(GPIOB, GPIO_PIN_1);

    HAL_GPIO_DeInit(GPIOE, GPIO_PIN_7|GPIO_PIN_9|GPIO_PIN_13);

    /* ADC3 DMA DeInit */
    HAL_DMA_DeInit(adcHandle->DMA_Handle);

    /* ADC3 interrupt Deinit */
    HAL_NVIC_DisableIRQ(ADC3_IRQn);
  }
  else if(adcHandle->Instance==ADC4)
  {
    /* Peripheral clock disable */
    HAL_RCC_ADC345_CLK_ENABLED--;
    if(HAL_RCC_ADC345_CLK_ENABLED==0){
      __HAL_RCC_ADC345_CLK_DISABLE();
    }

    /**ADC4 GPIO Configuration
    PE14     ------> ADC4_IN1
    PE15     ------> ADC4_IN2
    PB12     ------> ADC4_IN3
    PB14     ------> ADC4_IN4
    */
    HAL_GPIO_DeInit(GPIOE, GPIO_PIN_14|GPIO_PIN_15);

    HAL_GPIO_DeInit(GPIOB, GPIO_PIN_12|GPIO_PIN_14);

    /* ADC4 DMA DeInit */
    HAL_DMA_DeInit(adcHandle->DMA_Handle);

    /* ADC4 interrupt Deinit */
    HAL_NVIC_DisableIRQ(ADC4_IRQn);
  }
  else if(adcHandle->Instance==ADC5)
  {
    /* Peripheral clock disable */
    HAL_RCC_ADC345_CLK_ENABLED--;
    if(HAL_RCC_ADC345_CLK_ENABLED==0){
      __HAL_RCC_ADC345_CLK_DISABLE();
    }

    /**ADC5 GPIO Configuration
    PA8     ------> ADC5_IN1
    */
    HAL_GPIO_DeInit(BATT_SAMPLE_GPIO_Port, BATT_SAMPLE_Pin);

  }
}

/* USER CODE BEGIN 1 */

// External references to flags in main.c
extern volatile uint32_t adc_ready_mask;
extern volatile uint8_t ready_half[4];
extern volatile uint32_t irq_events;
extern volatile uint32_t irq_count_adc[4];

void HAL_ADC_ConvHalfCpltCallback(ADC_HandleTypeDef *hadc)
{
  // First half of DMA buffer (samples 0-1023) complete
  // Set bit [0-3]: Half-complete flags for ADC1-4
    
  if (hadc->Instance == ADC1) {
    adc_ready_mask |= (1 << 0);  // ADC1 half-complete
    adc_half_ready = 1;
    ready_half[0] = 0;  // First half
    irq_events++;
    irq_count_adc[0]++;
  }
  else if (hadc->Instance == ADC2) {
    adc_ready_mask |= (1 << 1);  // ADC2 half-complete
    ready_half[1] = 0;
    irq_events++;
    irq_count_adc[1]++;
  }
  else if (hadc->Instance == ADC3) {
    adc_ready_mask |= (1 << 2);  // ADC3 half-complete
    ready_half[2] = 0;
    irq_events++;
    irq_count_adc[2]++;
  }
  else if (hadc->Instance == ADC4) {
    adc_ready_mask |= (1 << 3);  // ADC4 half-complete
    ready_half[3] = 0;
    irq_events++;
    irq_count_adc[3]++;
  }
}

void HAL_ADC_ConvCpltCallback(ADC_HandleTypeDef *hadc)
{
  // Full DMA buffer (samples 1024-2047) complete, circular restart at 0
  // Set bit [4-7]: Full-complete flags for ADC1-4
    
  if (hadc->Instance == ADC1) {
    adc_ready_mask |= (1 << 4);  // ADC1 full-complete
    adc_full_ready = 1;
    ready_half[0] = 1;  // Second half
    irq_events++;
    irq_count_adc[0]++;
  }
  else if (hadc->Instance == ADC2) {
    adc_ready_mask |= (1 << 5);  // ADC2 full-complete
    ready_half[1] = 1;
    irq_events++;
    irq_count_adc[1]++;
  }
  else if (hadc->Instance == ADC3) {
    adc_ready_mask |= (1 << 6);  // ADC3 full-complete
    ready_half[2] = 1;
    irq_events++;
    irq_count_adc[2]++;
  }
  else if (hadc->Instance == ADC4) {
    adc_ready_mask |= (1 << 7);  // ADC4 full-complete
    ready_half[3] = 1;
    irq_events++;
    irq_count_adc[3]++;
  }
}

/* USER CODE END 1 */
