iluvpomeranians/Acoustic_Imager/testing/SPI_tests/SPI_test_multiple_loop_throughput_with_FFTframe.py

import spidev
import time
import zlib
import sys
import struct
import csv
import resource
import numpy as np
import matplotlib.pyplot as plt
from pathlib import Path

# If you don't need FFTFrame for this sweep test, you can remove these two lines.
sys.path.append(str(Path(__file__).resolve().parents[1] / "dataframe"))
from fftframe import FFTFrame  # noqa: F401

# ---------------------------
# Config
# ---------------------------
N_MICS = 16
SAMPLE_RATE_HZ = 100000
SAMPLES_PER_CHANNEL = 1024

# rFFT bins for real FFT: N/2 + 1
N_BINS = SAMPLES_PER_CHANNEL // 2 + 1  # 513

FPS_TARGET = 30
CHUNK = 4096
DURATION_S = 5  # per-speed test duration (seconds)

LIMIT_30_FPS_MODE = False   # False = unthrottled
CRC_EVERY_N = 1             # set to 1 during sweep to find corruption cliff

SWEEP_MHZ_START = 30
SWEEP_MHZ_END = 120
SWEEP_MHZ_STEP = 10

# ---------------------------
# Frame format
# ---------------------------
MAGIC_START = 0x46524654  # arbitrary stable tag
MAGIC_END   = 0x454E4421  # 'END!'

VERSION = 1

# Little-endian header:
# magic(u32), ver(u16), hdr_len(u16),
# seq(u32),
# mic_count(u16), fft_size(u16),
# sample_rate(u32),
# bins(u16), reserved(u16),
# payload_len(u32)
HEADER_FMT = "<IHH I HH I HH I"
HEADER_LEN = struct.calcsize(HEADER_FMT)

# Trailer: crc32(u32), end_magic(u32)
TRAILER_FMT = "<II"
TRAILER_LEN = struct.calcsize(TRAILER_FMT)

PAYLOAD_LEN = N_MICS * N_BINS * 4  # float32
FRAME_BYTES = HEADER_LEN + PAYLOAD_LEN + TRAILER_LEN
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
